SpicyWiener69/RaspberryPiChessComputerSystem/UI/lvgl/docs/src/_static/images/clip_corner_2_result.png

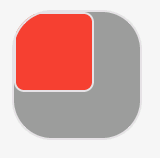
UI/lvgl/docs/src/_static/images/clip_corner_2_result.png
