SpicyWiener69/RaspberryPiChessComputerSystem/UI/lvgl/tests/ref_imgs/draw/render/al88/demo_render_blend_mode_opa_128.png

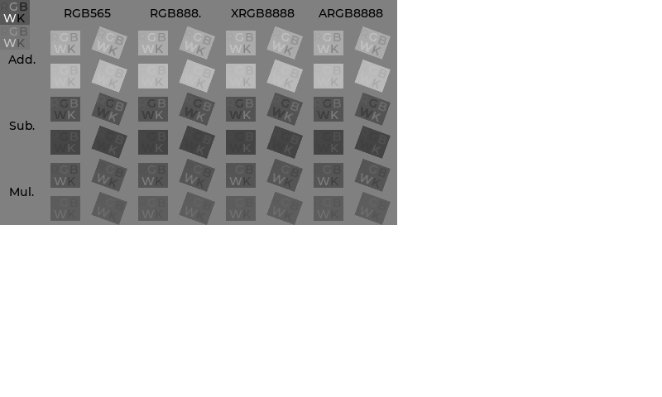
UI/lvgl/tests/ref_imgs/draw/render/al88/demo_render_blend_mode_opa_128.png
