SpicyWiener69/RaspberryPiChessComputerSystem/UI/lvgl/tests/ref_imgs/draw/render/al88/demo_render_conical_gradient_opa_255.png

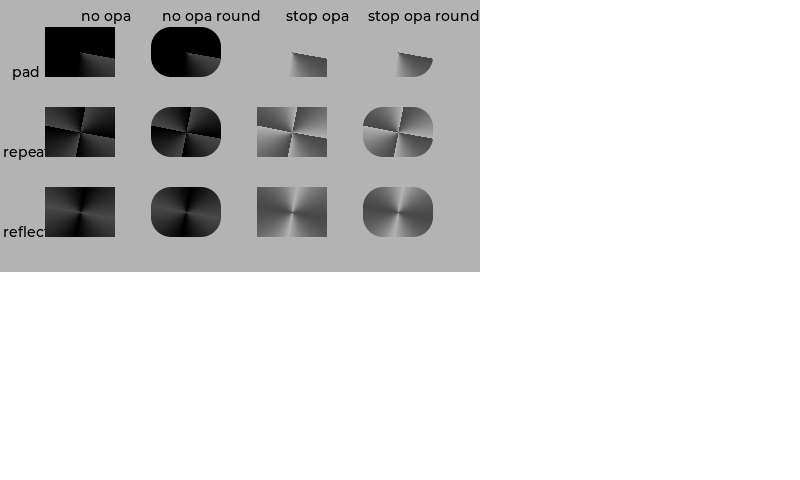
UI/lvgl/tests/ref_imgs/draw/render/al88/demo_render_conical_gradient_opa_255.png
