SpicyWiener69/RaspberryPiChessComputerSystem/UI/lvgl/tests/ref_imgs/draw/render/argb8888/demo_render_image_recolor_1_opa_128.png

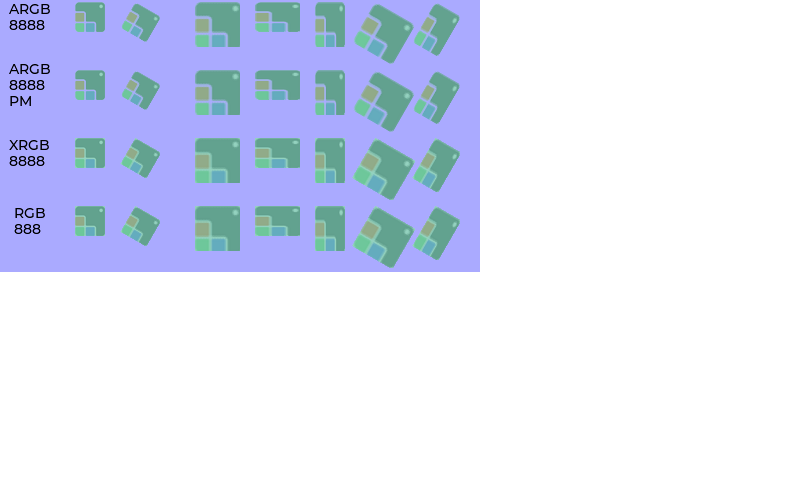
UI/lvgl/tests/ref_imgs/draw/render/argb8888/demo_render_image_recolor_1_opa_128.png
