SpicyWiener69/RaspberryPiChessComputerSystem/UI/lvgl/tests/ref_imgs/draw/render/argb8888/demo_render_text_opa_128.png

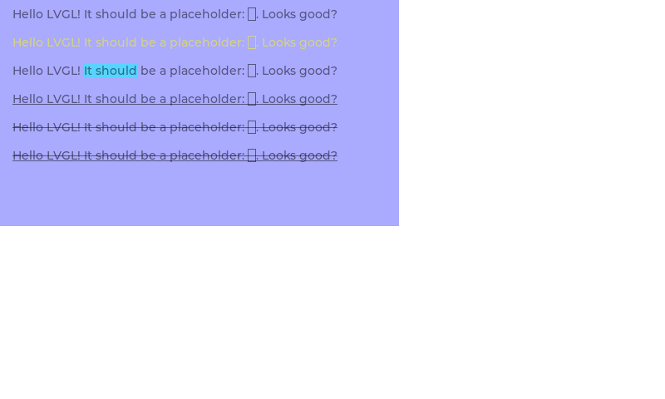
UI/lvgl/tests/ref_imgs/draw/render/argb8888/demo_render_text_opa_128.png
