SpicyWiener69/RaspberryPiChessComputerSystem/UI/lvgl/tests/ref_imgs/draw/render/argb8888_premultiplied/demo_render_arc_normal_opa_255.png

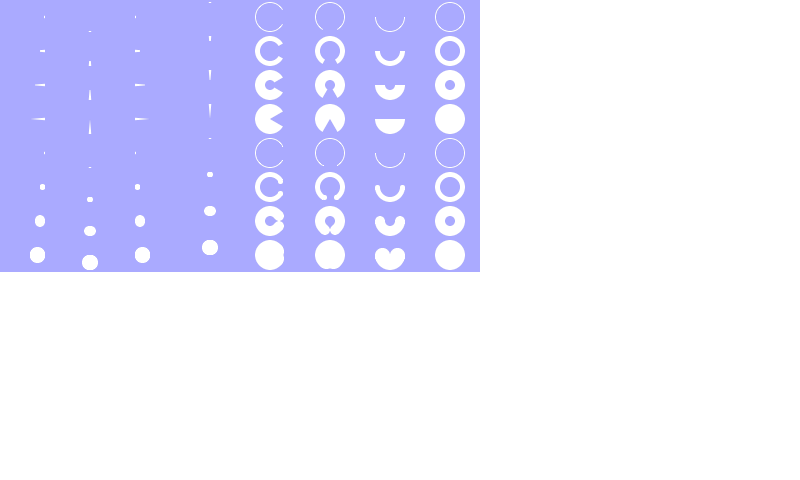
UI/lvgl/tests/ref_imgs/draw/render/argb8888_premultiplied/demo_render_arc_normal_opa_255.png
