SpicyWiener69/RaspberryPiChessComputerSystem/UI/lvgl/tests/ref_imgs/draw/render/i1/demo_render_border_opa_192.png

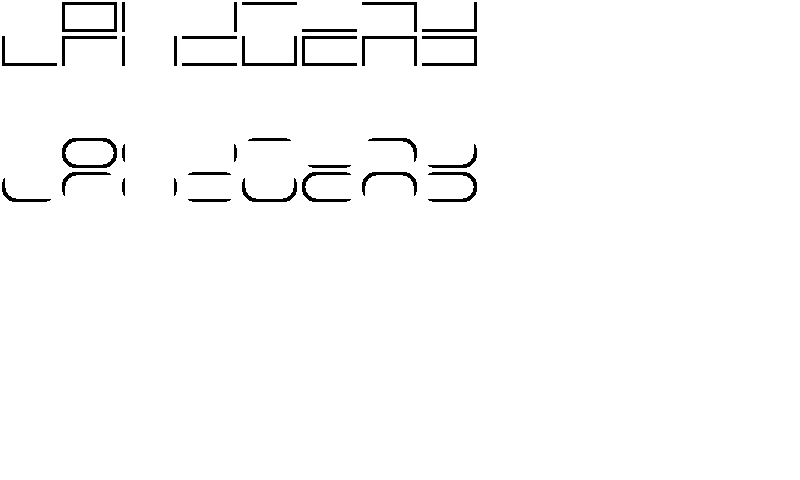
UI/lvgl/tests/ref_imgs/draw/render/i1/demo_render_border_opa_192.png
