SpicyWiener69/RaspberryPiChessComputerSystem/UI/lvgl/tests/ref_imgs/draw/render/i1/demo_render_image_recolor_3_opa_255.png

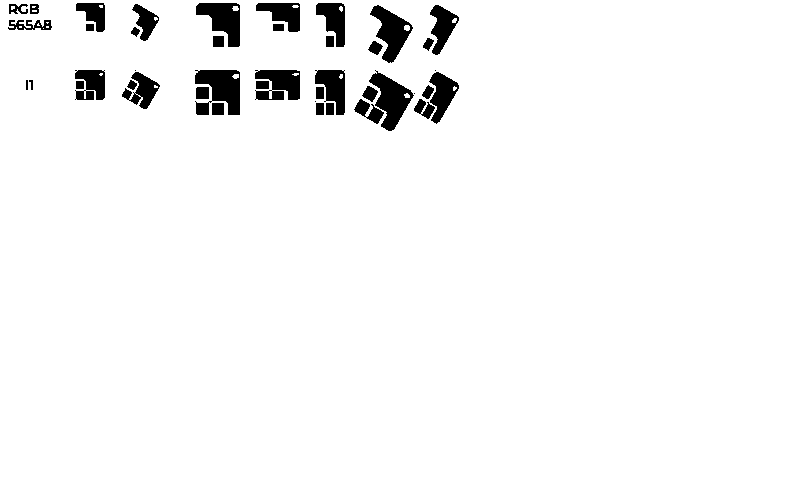
UI/lvgl/tests/ref_imgs/draw/render/i1/demo_render_image_recolor_3_opa_255.png
