SpicyWiener69/RaspberryPiChessComputerSystem/UI/lvgl/tests/ref_imgs/draw/render/l8/demo_render_box_shadow_opa_255.png

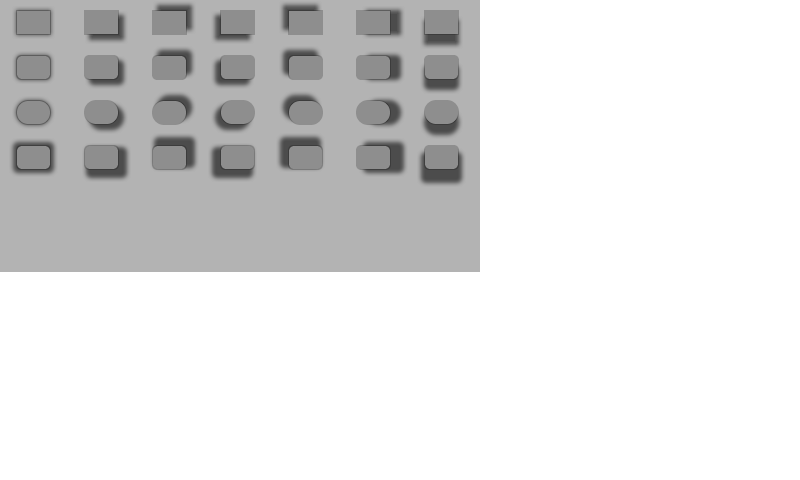
UI/lvgl/tests/ref_imgs/draw/render/l8/demo_render_box_shadow_opa_255.png
