SpicyWiener69/RaspberryPiChessComputerSystem/UI/lvgl/tests/ref_imgs_vg_lite/draw/render/argb1555/demo_render_border_opa_128.png

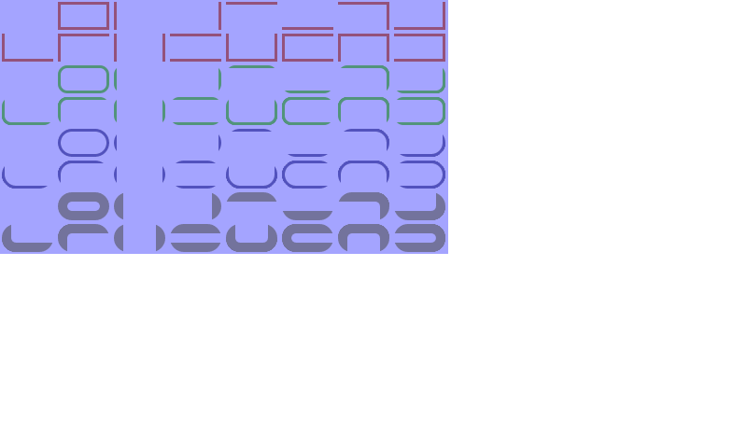
UI/lvgl/tests/ref_imgs_vg_lite/draw/render/argb1555/demo_render_border_opa_128.png
