SpicyWiener69/RaspberryPiChessComputerSystem/UI/lvgl/tests/ref_imgs_vg_lite/draw/render/argb2222/demo_render_line_opa_255.png

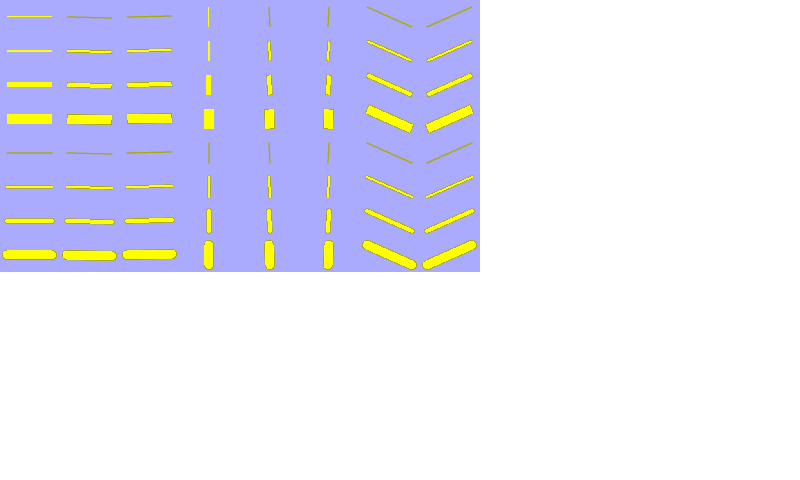
UI/lvgl/tests/ref_imgs_vg_lite/draw/render/argb2222/demo_render_line_opa_255.png
