SpicyWiener69/RaspberryPiChessComputerSystem/UI/lvgl/tests/ref_imgs_vg_lite/draw/render/argb8888/demo_render_line_opa_128.png

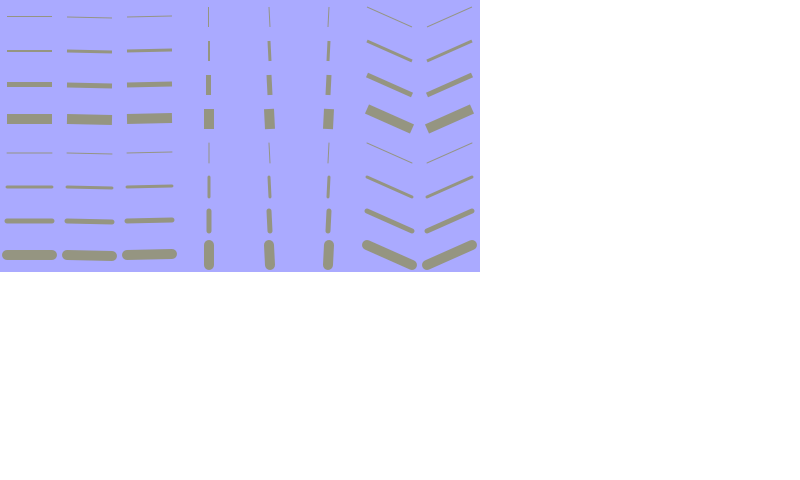
UI/lvgl/tests/ref_imgs_vg_lite/draw/render/argb8888/demo_render_line_opa_128.png
