SpicyWiener69/RaspberryPiChessComputerSystem/UI/lvgl/tests/ref_imgs_vg_lite/draw/render/argb8888_premultiplied/demo_render_triangle_opa_128.png

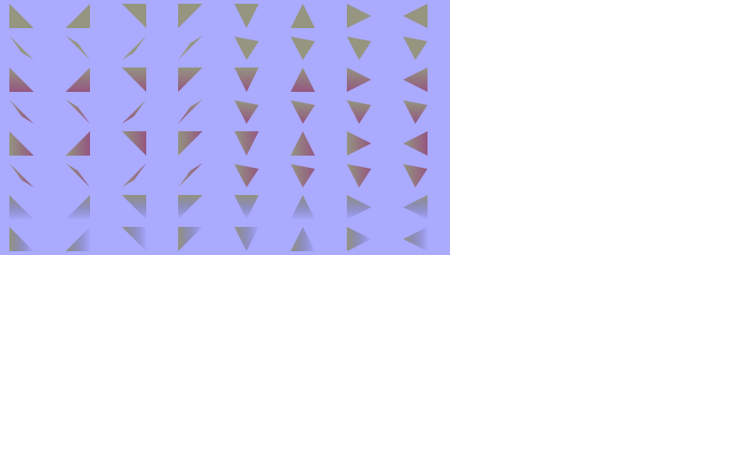
UI/lvgl/tests/ref_imgs_vg_lite/draw/render/argb8888_premultiplied/demo_render_triangle_opa_128.png
