SpicyWiener69/RaspberryPiChessComputerSystem/UI/src/main.cpp

/*******************************************************************
 *
 * main.c - LVGL simulator for GNU/Linux
 *
 * Based on the original file from the repository
 *
 * @note eventually this file won't contain a main function and will
 * become a library supporting all major operating systems
 *
 * To see how each driver is initialized check the
 * 'src/lib/display_backends' directory
 *
 * - Clean up
 * - Support for multiple backends at once
 *   2025 EDGEMTech Ltd.
 *
 * Author: EDGEMTech Ltd, Erik Tagirov (erik.tagirov@edgemtech.ch)
 *
 ******************************************************************/
#include <unistd.h>
#include <pthread.h>
#include <stdio.h>
#include <stdlib.h>
#include <string.h>
#include <cassert>

#include "lvgl/lvgl.h"
#include "lvgl/demos/lv_demos.h"

#include "src/lib/driver_backends.h"
#include "src/lib/simulator_util.h"
#include "src/lib/simulator_settings.h"


#include "src/ui.h"
#include "src/socket_server.h"

#include <cassert>
#include <iostream>
#include <string>
#include <vector>

/* Internal functions */
static std::vector<std::string> split(const std::string& s, char delim);
static void server_msg_cb(const char *msg, size_t len, void *user_data);
static void configure_simulator(int argc, char **argv);
static void print_lvgl_version(void);
static void print_usage(void);
static void ui_shutdown(void);


void poll_timer(lv_timer_t * timer);

/* contains the name of the selected backend if user
 * has specified one on the command line */ 
static char *selected_backend; /* Global simulator settings, defined in lv_linux_backend.c */
extern simulator_settings_t settings;


/**
 * @brief Print LVGL version
 */
static void print_lvgl_version(void)
{
    fprintf(stdout, "%d.%d.%d-%s\n",
            LVGL_VERSION_MAJOR,
            LVGL_VERSION_MINOR,
            LVGL_VERSION_PATCH,
            LVGL_VERSION_INFO);
}

/**
 * @brief Print usage information
 */
static void print_usage(void)
{
    fprintf(stdout, "\nlvglsim [-V] [-B] [-b backend_name] [-W window_width] [-H window_height]\n\n");
    fprintf(stdout, "-V print LVGL version\n");
    fprintf(stdout, "-B list supported backends\n");
}

/**
 * @brief Configure simulator
 * @description process arguments recieved by the program to select
 * appropriate options
 * @param argc the count of arguments in argv
 * @param argv The arguments
 */
static void configure_simulator(int argc, char **argv)
{
    int opt = 0;

    selected_backend = NULL;
    driver_backends_register();

    const char *env_w = getenv("LV_SIM_WINDOW_WIDTH");
    const char *env_h = getenv("LV_SIM_WINDOW_HEIGHT");
    /* Default values */
    settings.window_width = atoi(env_w ? env_w : "800");
    settings.window_height = atoi(env_h ? env_h : "480");

    /* Parse the command-line options. */
    while ((opt = getopt (argc, argv, "b:fmW:H:BVh")) != -1) {
        switch (opt) {
        case 'h':
            print_usage();
            exit(EXIT_SUCCESS);
            break;
        case 'V':
            print_lvgl_version();
            exit(EXIT_SUCCESS);
            break;
        case 'B':
            driver_backends_print_supported();
            exit(EXIT_SUCCESS);
            break;
        case 'b':
            if (driver_backends_is_supported(optarg) == 0) {
                die("error no such backend: %s\n", optarg);
            }
            selected_backend = strdup(optarg);
            break;
        case 'W':
            settings.window_width = atoi(optarg);
            break;
        case 'H':
            settings.window_height = atoi(optarg);
            break;
        case ':':
            print_usage();
            die("Option -%c requires an argument.\n", optopt);
            break;
        case '?':
            print_usage();
            die("Unknown option -%c.\n", optopt);
        }
    }
}

/**
 * @brief entry point
 * @description start a demo
 * @param argc the count of arguments in argv
 * @param argv The arguments
 */
int main(int argc, char **argv)
{   
    configure_simulator(argc, argv);

    /* Initialize LVGL. */
    lv_init();
    
	    /* Initialize the configured backend */
    if (driver_backends_init_backend(selected_backend) == -1) {
        die("Failed to initialize display backend");
    }

    /* Enable for EVDEV support */
#if LV_USE_EVDEV
    if (driver_backends_init_backend("EVDEV") == -1) {
        die("Failed to initialize evdev");
    }
#endif
    if (server_init(server_msg_cb, NULL) != 0){
        die("error init server");
    }

    lv_timer_t* timer = lv_timer_create(poll_timer, 500,  NULL);
    lv_obj_clean(lv_screen_active());
    
    init_ui();
    std::string str;
    str  = "rnbqkbnr/pppppppp/8/8/8/8/PPPPPPPP/RNBQKBNR";
    draw_fen(str);
    driver_backends_run_loop();
    return 0;
}
 
static void server_msg_cb(const char* msg, size_t len, void* user_data) {
    std::string str (msg,len);
    if (str == "quit\n"){
        ui_shutdown();
    }
    std::cout << "recieved:" << str << '\n';
    auto parts = split(str,';');
    if (parts[0] == "fen")
        draw_fen(parts[1]);
    else if (parts[0] == "redo"){
        warning_ui_toggle(true);
    }
    else if (parts[0] == "resume"){
        warning_ui_toggle(false);
    }
    else{
        assert(false && "Unknown message type");
    }
}

void poll_timer(lv_timer_t * timer)
{
  /* Use the user_data */
  socket_poll();
  std::cout << "server polled"<<'\n';
  //uint32_t * user_data = static_cast<uint32_t *>(lv_timer_get_user_data(timer));
  
  /* Do something with LVGL */  
}

static void ui_shutdown(void){
    std::cout << "shutting down..." << std::endl;
    server_deinit();
    exit(0);
}

static std::vector<std::string> split(const std::string& s, char delim) {
    std::vector<std::string> result;
    std::string current;
    for (char c : s) {
        if (c == delim) {
            result.push_back(current);
            current.clear();
        } else {
            current += c;
        }
    }
    result.push_back(current); // last token
    return result;
}
