SpicyWiener69/RaspberryPiChessComputerSystem/UI/src/ui.h

/**
 * @file ui.h
 *
 * Chess ui definitions
 *
 * Author: 
 *
 */
#ifndef UI_H
#define UI_H


#include <string>
#include "lvgl.h"

void init_ui(void);


/* === WARNING UI EXTERNAL FUNCTIONS ============================ */

void warning_ui_toggle(bool show); 

/* === GRID UI EXTERNAL FUNCTIONS ============================ */

void draw_fen(std::string fen);

//void board_grid_ui(void);


/* === MENU UI EXTERNAL FUNCTIONS ============================ */

//void chess_settings_menu_ui(void);
//void open_menu_ui(void);


/* === DEFINITIONS ============================ */


// typedef enum{
//     NONE,
//     BLACK,
//     WHITE
// }Side;

typedef struct{
    bool computer_playing;
    int engine_timeout;
    int engine_strength;
    int side; // 0 is black, 1 is white
    bool auto_mover;
}GameSettings;









#endif 
